RobertPHeller/NewBikeComputer/NewBikeComputer/SerialCLI.cpp

// -!- C++ -!- //////////////////////////////////////////////////////////////
//
//  System        : 
//  Module        : 
//  Object Name   : $RCSfile$
//  Revision      : $Revision$
//  Date          : $Date$
//  Author        : $Author$
//  Created By    : Robert Heller
//  Created       : Sun Sep 15 17:56:32 2013
//  Last Modified : <221017.1648>
//
//  Description	
//
//  Notes
//
//  History
//	
/////////////////////////////////////////////////////////////////////////////
//
//  Copyright (c) 2013 Deepwoods Software.
// 
//  All Rights Reserved.
// 
// This  document  may  not, in  whole  or in  part, be  copied,  photocopied,
// reproduced,  translated,  or  reduced to any  electronic  medium or machine
// readable form without prior written consent from Deepwoods Software.
//
//////////////////////////////////////////////////////////////////////////////

static const char rcsid[] = "@(#) : $Id$";

#include <Arduino.h>
#include <stdio.h>
#include "SerialCLI.h"
#include <ctype.h>
#include "PersistentTripDatabase.h"
#include "BikeNVS.h"
#include "Wheelsensor.h"
#include "SPIFFS.h"

static const char *HelpText[] = {
    "New Bike Computer 1.0",
    "",
    "Commands:",
    "",
    "S offset",
    "  Set TZ offset",
    "U",
    "  Upload tripfile",
    "C",
    "  Clear tripfile",
    "Z",
    "  Zero NVS (miles, tzoffset)", 
    "L",
    "  List files",
    "H",
    "  Print this help",
    "",
    NULL
};

void ProcessSerialCLI(PersistentTripDatabase *PTD,BikeNVS *NVS,
                      Wheelsensor *wheel)
{
    char buffer[256];
    int len;
    
    if (Serial.available() > 0) {
        len = Serial.readBytesUntil('\r',buffer,sizeof(buffer)-1);
        Serial.println(buffer);
        if (len == 0) return;
        buffer[len] = '\0';
        //Serial.print("*** ProcessSerialCLI(): command is ");
        //Serial.println(toupper(buffer[0]));
        switch ((Commands) (toupper(buffer[0]))) {
        case SET:
            {
                char unused;
                int tz = 0;
                if (sscanf(buffer,"%c %d",&unused,&tz) != 2) {
                    Serial.println("Syntax error!");
                } else {
                    PTD->SetTZOffset(tz);
                    NVS->SetTZOffset(tz);
                    Serial.println("");
                    Serial.println("Time Zone set.");
                }
                break;
            }
        case CLEAR:
            {
                PTD->ZeroFile(wheel->Miles());
                Serial.println("");
                Serial.println("Trip File zeroed.");
                break;
            }
        case UPLOAD:
            {
                Serial.println("");
                Serial.println("--Uploading File--");
                PTD->UploadFile();
                Serial.println("--UploadComplete--");
                break;
            }
        case ZERO:
            {
                wheel->ZeroMiles();
                NVS->SetMiles(0.0);
                PTD->SetTZOffset(0);
                NVS->SetTZOffset(0);
                NVS->commit();
                Serial.println("");
                Serial.println("EEProm cleared.");
                break;
            }
        case LIST:
            {
                char buffer[128];
                int count = 0;
                Serial.println("");
                //Serial.print("*** ProcessSerialCLI() [LIST]: count initialized to ");
                //Serial.println(count);
                File root = SPIFFS.open("/spiffs");
                if (!root)
                {
                    Serial.println("Cannot open root file system directory!");
                    break;
                }
                File f;
                while (f = root.openNextFile())
                {
                    snprintf(buffer,sizeof(buffer),"%c %5d %s",
                             f.isDirectory()? 'd': ' ',
                             f.size(),
                             f.name());
                    Serial.println(buffer);
                    count++;
                    f.close();
                }
                root.close();
                snprintf(buffer,sizeof(buffer),"%d files",count);
                Serial.println(buffer);
            }
            break;
        case REMOVE:
            SPIFFS.remove("/spiffs/trips.list");
            SPIFFS.end();
            PTD->begin(wheel->Miles(),NVS->TZOffset());
            break;
        case FORMAT:
            SPIFFS.end();
            SPIFFS.format();
            PTD->begin(wheel->Miles(),NVS->TZOffset());
            break;
        case DUMP:
            snprintf(buffer,sizeof(buffer),"Miles: %f, TZ: %d",NVS->Miles(),NVS->TZOffset());
            Serial.println(buffer);
            break;
        case HELP:
            {
                Serial.println("");
                int i, n = sizeof(HelpText) / sizeof(HelpText[0]);
                for (i = 0; i < n && HelpText[i]; i++) {
                    Serial.println(HelpText[i]);
                }
                break;
            }
        default:
            Serial.println("");
            Serial.println("Unknown Command.");
        }
        Serial.print(">>");
        Serial.flush();
    }
}               
            
